sporkus/bully2040_keyboard/kicad/pcb/bully.kicad_sch

## KiCad design kicad/pcb/bully.kicad_sch (2023-07-27)

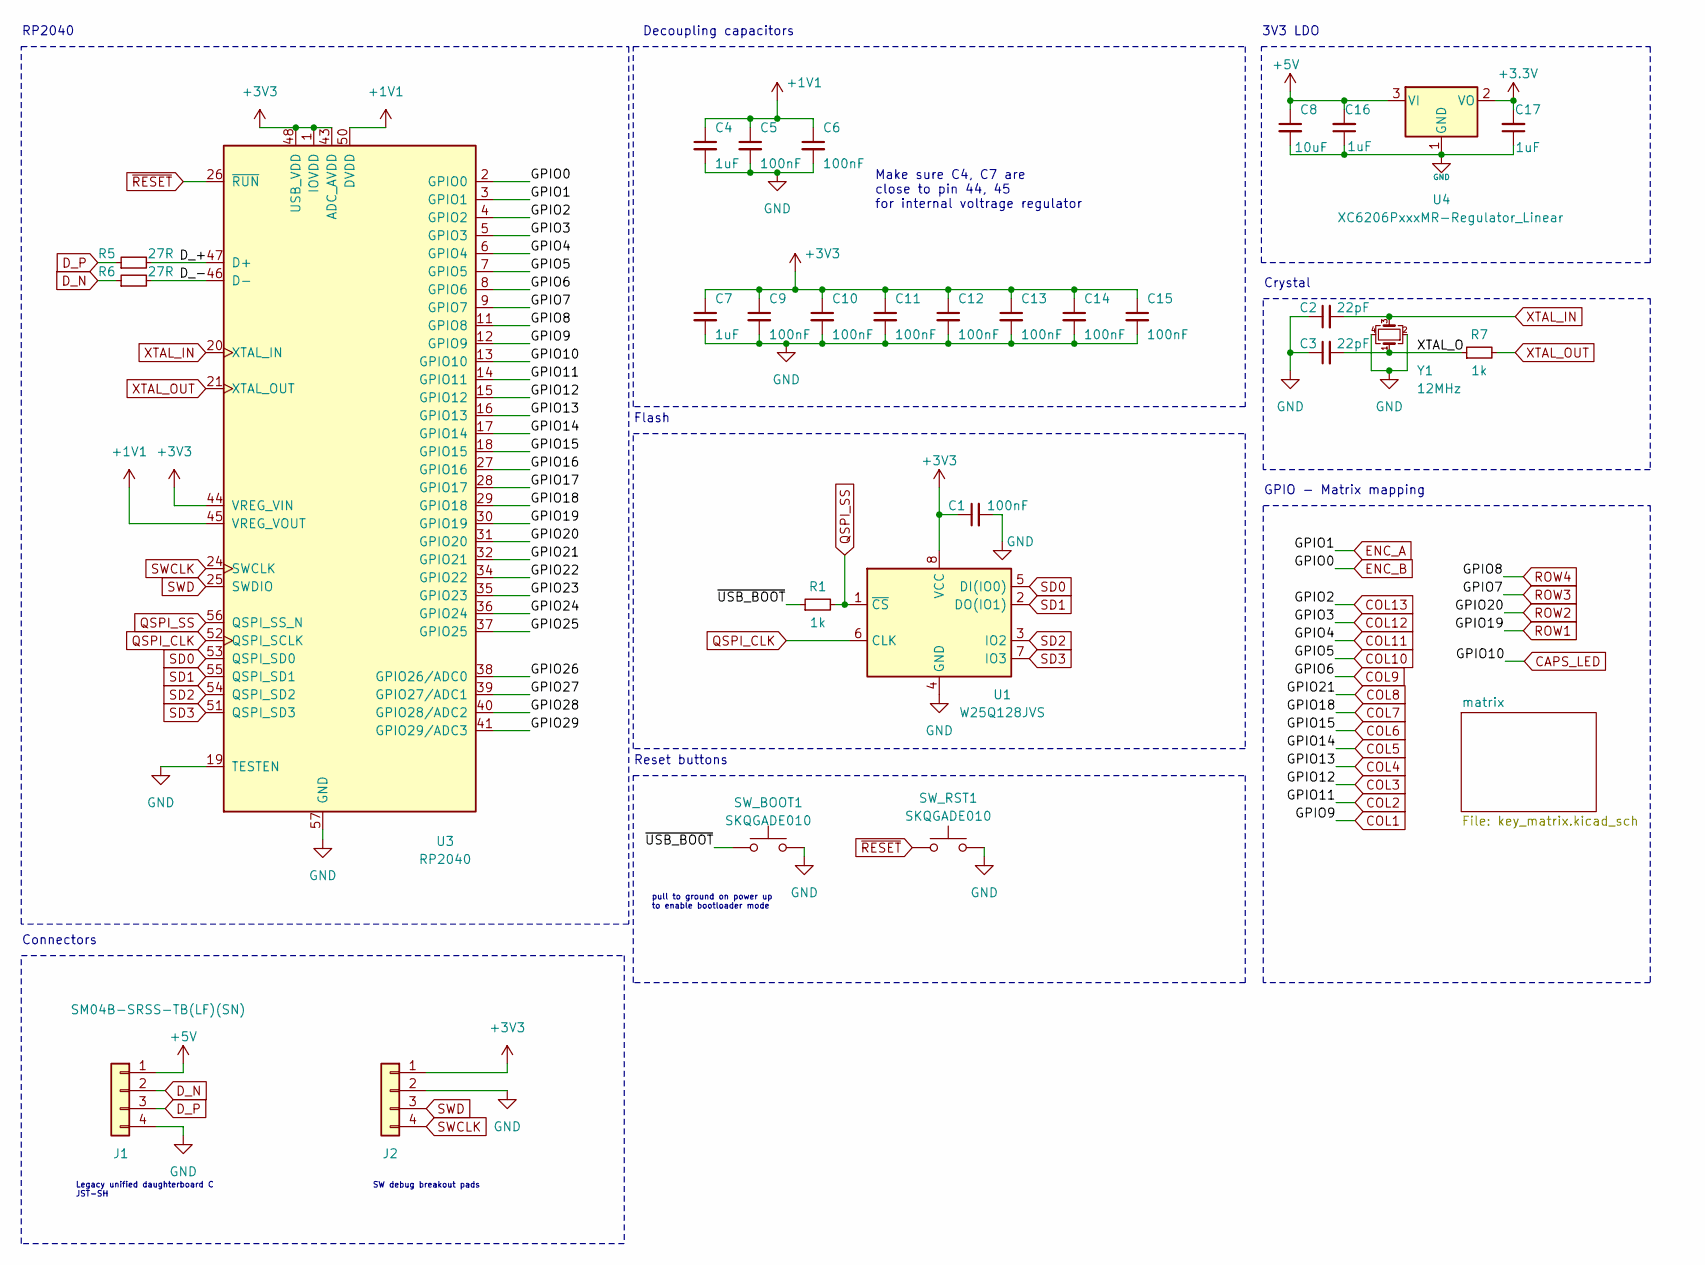
[picture p10: schematic bully.kicad_sch]

Parts:
C1, C5, C6, C9, C10, C11, C12, C13, C14, C15: 100nF; C_0402_1005Metric
C2, C3: 22pF; C_0402_1005Metric
C4, C7, C16, C17: 1uF; C_0402_1005Metric
C8: 10uF; C_0402_1005Metric
J1: SM04B-SRSS-TB(LF)(SN); JST-SR-4; JlcPosOffset 0, -2.6
J2: Conn_01x04; PinHeader_1x04_P2.54mm_Vertical
R1, R7: 1k; R_0402_1005Metric
R5, R6: 27R; R_0402_1005Metric
SW_BOOT1: SKQGADE010; SW_SPST_SKQG_WithoutStem; LCSC C116647
SW_RST1: SKQGADE010; SW_SPST_SKQG_WithoutStem; LCSC C116647
U1: W25Q128JVS; SOIC-8_5.23x5.23mm_P1.27mm; LCSC C97521
U3: RP2040; RP2040-QFN-56; LCSC C2040
U4: XC6206PxxxMR-Regulator_Linear; SOT-23; LCSC C5446
Y1: 12MHz; Crystal_SMD_3225-4Pin_3.2x2.5mm; LCSC C9002

Connections:
+1V1: C4.1, C5.1, C6.1, U3.23 (DVDD), U3.45 (VREG_VOUT), U3.50 (DVDD)
+3.3V: C17.2, U4.2 (VO)
+3V3: C1.1, C7.1, C9.1, C10.1, C11.1, C12.1, C13.1, C14.1, C15.1, J2.1, U1.8 (VCC), U3.1 (IOVDD), U3.10 (IOVDD), U3.22 (IOVDD), U3.33 (IOVDD), U3.42 (IOVDD), U3.43 (ADC_AVDD), U3.44 (VREG_VIN), U3.48 (USB_VDD), U3.49 (IOVDD)
+5V: C8.1, C16.2, J1.1, U4.3 (VI)
CAPS_LED: U3.13 (GPIO10)
COL1: U3.12 (GPIO9)
COL2: U3.14 (GPIO11)
COL3: U3.15 (GPIO12)
COL4: U3.16 (GPIO13)
COL5: U3.17 (GPIO14)
COL6: U3.18 (GPIO15)
COL7: U3.29 (GPIO18)
COL8: U3.32 (GPIO21)
COL9: U3.8 (GPIO6)
COL10: U3.7 (GPIO5)
COL11: U3.6 (GPIO4)
COL12: U3.5 (GPIO3)
COL13: U3.4 (GPIO2)
D_+: R5.2, U3.47 (D+)
D_-: R6.2, U3.46 (D-)
D_N: J1.2, R6.1
D_P: J1.3, R5.1
ENC_A: U3.3 (GPIO1)
ENC_B: U3.2 (GPIO0)
GND: C1.2, C2.1, C3.1, C4.2, C5.2, C6.2, C7.2, C8.2, C9.2, C10.2, C11.2, C12.2, C13.2, C14.2, C15.2, C16.1, C17.1, J1.4, J2.2, SW_BOOT1.1, SW_RST1.1, U1.4 (GND), U3.19 (TESTEN), U3.57 (GND), U4.1 (GND), Y1.2, Y1.4
GPIO16: U3.27 (GPIO16)
GPIO17: U3.28 (GPIO17)
GPIO22: U3.34 (GPIO22)
GPIO23: U3.35 (GPIO23)
GPIO24: U3.36 (GPIO24)
GPIO25: U3.37 (GPIO25)
GPIO26: U3.38 (GPIO26/ADC0)
GPIO27: U3.39 (GPIO27/ADC1)
GPIO28: U3.40 (GPIO28/ADC2)
GPIO29: U3.41 (GPIO29/ADC3)
QSPI_CLK: U1.6 (CLK), U3.52 (QSPI_SCLK)
QSPI_SS: R1.2, U1.1 (~CS), U3.56 (QSPI_SS_N)
ROW1: U3.30 (GPIO19)
ROW2: U3.31 (GPIO20)
ROW3: U3.9 (GPIO7)
ROW4: U3.11 (GPIO8)
SD0: U1.5 (DI(IO0)), U3.53 (QSPI_SD0)
SD1: U1.2 (DO(IO1)), U3.55 (QSPI_SD1)
SD2: U1.3 (IO2), U3.54 (QSPI_SD2)
SD3: U1.7 (IO3), U3.51 (QSPI_SD3)
SWCLK: J2.4, U3.24 (SWCLK)
SWD: J2.3, U3.25 (SWDIO)
XTAL_IN: C2.2, U3.20 (XTAL_IN), Y1.3
XTAL_O: C3.2, R7.1, Y1.1
XTAL_OUT: R7.2, U3.21 (XTAL_OUT)
~RESET: SW_RST1.2, U3.26 (~RUN)
~USB_BOOT: R1.1, SW_BOOT1.2

Notes on the sheet:
pull to ground on power up to enable bootloader mode
SW debug breakout pads
Legacy unified daughterboard C JST-SH
Flash
RP2040
3V3 LDO
GPIO - Matrix mapping
Decoupling capacitors
Connectors
Make sure C4, C7 are close to pin 44, 45 for internal voltrage regulator
Crystal
Reset buttons
