sporkus/bully2040_keyboard/kicad/pcb/key_matrix.kicad_sch

## KiCad design kicad/pcb/key_matrix.kicad_sch (2023-07-27)

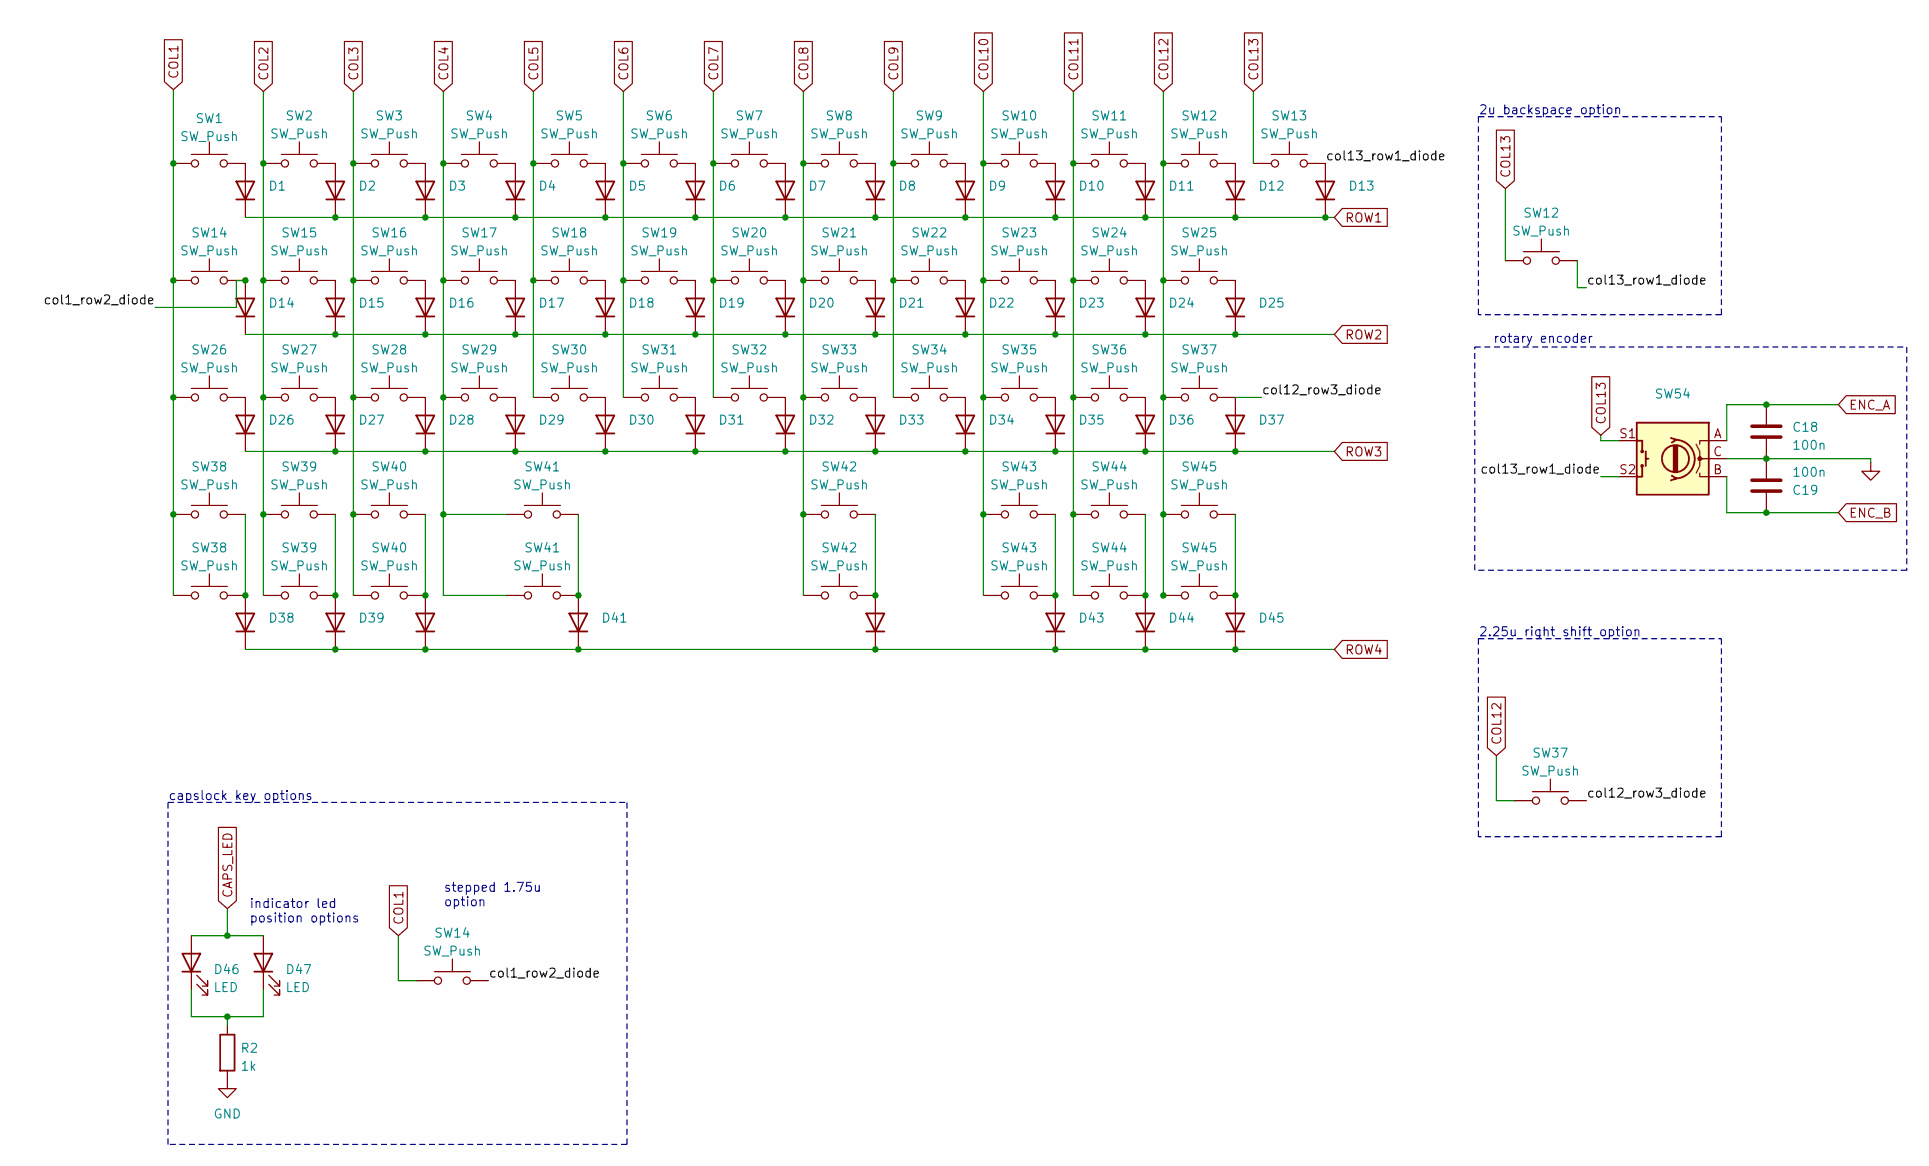
[picture p11: schematic key_matrix.kicad_sch]

Parts:
C18, C19: 100n; C_0402_1005Metric
D1, D2, D3, D4, D5, D6, D7, D8, D9, D10, D11, D12, D13, D14, D15, D16, D17, D18, D19, D20, D21, D22, D23, D24, D25, D26, D27, D28, D29, D30, D31, D32, D33, D34, D35, D36, D37, D38, D39, D40, D41, D42, D43, D44, D45: 1N4148W; D_SOD-123; LCSC C81598
D46, D47: LED; LED_0805_2012Metric_Pad1.15x1.40mm_HandSolder
R2: 1k; R_0805_2012Metric
SW1, SW40: SW_Push; MX-Alps-Hybrid-1.5U
SW2, SW3, SW4, SW5, SW6, SW7, SW8, SW9, SW10, SW11, SW12, SW13, SW15, SW16, SW17, SW18, SW19, SW20, SW21, SW22, SW23, SW24, SW27, SW28, SW29, SW30, SW31, SW32, SW33, SW34, SW35, SW36: SW_Push; MX-Alps-Hybrid-1U
SW14: SW_Push; MX-Solderable-1.25U
SW25: SW_Push; MX-Alps-Hybrid-1.75U
SW26, SW37: SW_Push; MX-Alps-Hybrid-2.25U
SW38, SW39, SW43, SW44, SW45: SW_Push; MX-Alps-Hybrid-1.25U
SW41, SW42: SW_Push; MX-Alps-Hybrid-3U-ReversedStabilizers
SW54: RotaryEncoder_Switch; RotaryEncoder_EC11

Connections:
CAPS_LED: D46.2 (A), D47.2 (A)
COL1: SW1.1, SW14.1, SW14.2, SW26.1, SW38.1
COL2: SW2.1, SW15.1, SW27.1, SW39.1, SW39.2
COL3: SW3.1, SW16.1, SW28.1, SW40.1, SW40.2
COL4: SW4.1, SW17.1, SW29.1, SW41.1
COL5: SW5.1, SW18.1, SW30.1
COL6: SW6.1, SW19.1, SW31.1
COL7: SW7.1, SW20.1, SW32.1
COL8: SW8.1, SW21.1, SW33.1, SW42.1, SW42.2
COL9: SW9.1, SW22.1, SW34.1
COL10: SW10.1, SW23.1, SW35.1, SW43.1, SW43.2
COL11: SW11.1, SW24.1, SW36.1, SW44.1, SW44.2
COL12: SW12.2, SW25.1, SW37.1, SW37.2, SW45.1
COL13: SW12.2, SW13.1, SW54.S1
ENC_A: C18.1, SW54.A
ENC_B: C19.1, SW54.B
GND: C18.2, C19.2, R2.2, SW54.C
unnamed: D1.2 (A), SW1.2
unnamed: D2.2 (A), SW2.2
unnamed: D3.2 (A), SW3.2
unnamed: D4.2 (A), SW4.2
unnamed: D5.2 (A), SW5.2
unnamed: D6.2 (A), SW6.2
unnamed: D7.2 (A), SW7.2
unnamed: D8.2 (A), SW8.2
unnamed: D9.2 (A), SW9.2
unnamed: D10.2 (A), SW10.2
unnamed: D11.2 (A), SW11.2
unnamed: D12.2 (A), SW12.1
unnamed: D15.2 (A), SW15.2
unnamed: D16.2 (A), SW16.2
unnamed: D17.2 (A), SW17.2
unnamed: D18.2 (A), SW18.2
unnamed: D19.2 (A), SW19.2
unnamed: D20.2 (A), SW20.2
unnamed: D21.2 (A), SW21.2
unnamed: D22.2 (A), SW22.2
unnamed: D23.2 (A), SW23.2
unnamed: D24.2 (A), SW24.2
unnamed: D25.2 (A), SW25.2
unnamed: D26.2 (A), SW26.2
unnamed: D27.2 (A), SW27.2
unnamed: D28.2 (A), SW28.2
unnamed: D29.2 (A), SW29.2
unnamed: D30.2 (A), SW30.2
unnamed: D31.2 (A), SW31.2
unnamed: D32.2 (A), SW32.2
unnamed: D33.2 (A), SW33.2
unnamed: D34.2 (A), SW34.2
unnamed: D35.2 (A), SW35.2
unnamed: D36.2 (A), SW36.2
unnamed: D38.2 (A), SW38.2
unnamed: D39.2 (A), SW39.1, SW39.2
unnamed: D40.2 (A), SW40.1, SW40.2
unnamed: D41.2 (A), SW41.2
unnamed: D42.2 (A), SW42.1, SW42.2
unnamed: D43.2 (A), SW43.1, SW43.2
unnamed: D44.2 (A), SW44.1, SW44.2
unnamed: D45.2 (A), SW45.2
unnamed: D46.1 (K), D47.1 (K), R2.1
ROW1: D1.1 (K), D2.1 (K), D3.1 (K), D4.1 (K), D5.1 (K), D6.1 (K), D7.1 (K), D8.1 (K), D9.1 (K), D10.1 (K), D11.1 (K), D12.1 (K), D13.1 (K)
ROW2: D14.1 (K), D15.1 (K), D16.1 (K), D17.1 (K), D18.1 (K), D19.1 (K), D20.1 (K), D21.1 (K), D22.1 (K), D23.1 (K), D24.1 (K), D25.1 (K)
ROW3: D26.1 (K), D27.1 (K), D28.1 (K), D29.1 (K), D30.1 (K), D31.1 (K), D32.1 (K), D33.1 (K), D34.1 (K), D35.1 (K), D36.1 (K), D37.1 (K)
ROW4: D38.1 (K), D39.1 (K), D40.1 (K), D41.1 (K), D42.1 (K), D43.1 (K), D44.1 (K), D45.1 (K)
col1_row2_diode: D14.2 (A), SW14.1, SW14.2
col12_row3_diode: D37.2 (A), SW37.1, SW37.2
col13_row1_diode: D13.2 (A), SW12.1, SW13.2, SW54.S2

Notes on the sheet:
rotary encoder
capslock key options
indicator led position options
2u backspace option
2.25u right shift option
stepped 1.75u option
